u1f992/qingpi/flex/flex_xl/flex_xl.kicad_sch

## KiCad design flex/flex_xl/flex_xl.kicad_sch (2023-11-06)

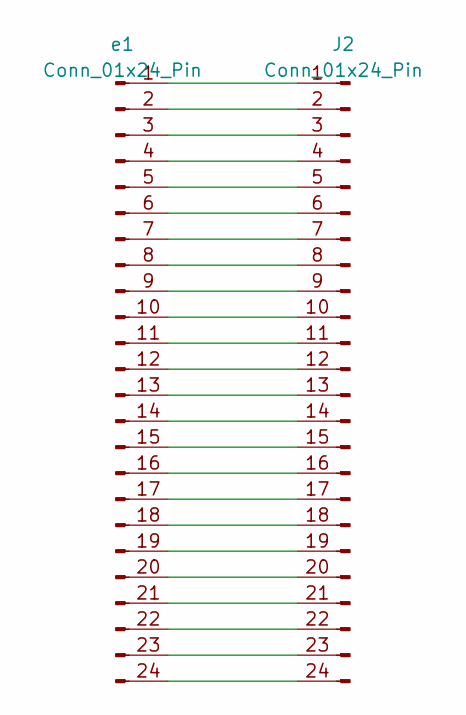
[picture p6: schematic flex_xl.kicad_sch]

Parts:
J2: Conn_01x24_Pin; THD0515-24CL-SN_FPC
e1: Conn_01x24_Pin; 3ds_xl

Connections:
unnamed: J2.1, e1.1
unnamed: J2.2, e1.2
unnamed: J2.3, e1.3
unnamed: J2.4, e1.4
unnamed: J2.5, e1.5
unnamed: J2.6, e1.6
unnamed: J2.7, e1.7
unnamed: J2.8, e1.8
unnamed: J2.9, e1.9
unnamed: J2.10, e1.10
unnamed: J2.11, e1.11
unnamed: J2.12, e1.12
unnamed: J2.13, e1.13
unnamed: J2.14, e1.14
unnamed: J2.15, e1.15
unnamed: J2.16, e1.16
unnamed: J2.17, e1.17
unnamed: J2.18, e1.18
unnamed: J2.19, e1.19
unnamed: J2.20, e1.20
unnamed: J2.21, e1.21
unnamed: J2.22, e1.22
unnamed: J2.23, e1.23
unnamed: J2.24, e1.24
